cslab-upm/smart-cover/firmware_ESP32/librerias/NTPClient/NTPClient.h

#pragma once

#include "Arduino.h"

#include <Udp.h>

#define SEVENZYYEARS 2208988800UL
#define NTP_PACKET_SIZE 48
#define NTP_DEFAULT_LOCAL_PORT 1337
#define LEAP_YEAR(Y)     ( (Y>0) && !(Y%4) && ( (Y%100) || !(Y%400) ) )


class NTPClient {
  private:
    UDP*          _udp;
    bool          _udpSetup       = false;

    const char*   _poolServerName = "pool.ntp.org"; // Default time server
    int           _port           = NTP_DEFAULT_LOCAL_PORT;
    int           _timeOffset     = 0;

    unsigned long _updateInterval = 60000;  // In ms

    unsigned long _currentEpoc    = 0;      // In s
    unsigned long _lastUpdate     = 0;      // In ms

    byte          _packetBuffer[NTP_PACKET_SIZE];

    void          sendNTPPacket();
    bool          isValid(byte * ntpPacket);

  public:
    NTPClient();
    NTPClient(UDP& udp);
    NTPClient(UDP& udp, int timeOffset);
    NTPClient(UDP& udp, const char* poolServerName);
    NTPClient(UDP& udp, const char* poolServerName, int timeOffset);
    NTPClient(UDP& udp, const char* poolServerName, int timeOffset, unsigned long updateInterval);
    void setUDPClient(UDP& udp);

    /**
     * Starts the underlying UDP client with the default local port
     */
    void begin();

    /**
     * Starts the underlying UDP client with the specified local port
     */
    void begin(int port);

    /**
     * This should be called in the main loop of your application. By default an update from the NTP Server is only
     * made every 60 seconds. This can be configured in the NTPClient constructor.
     *
     * @return true on success, false on failure
     */
    bool update();

    /**
     * This will force the update from the NTP Server.
     *
     * @return true on success, false on failure
     */
    bool forceUpdate();

	int getYear();
	int getDate();
	uint8_t getMonth(unsigned long secs);
    int getDay();
    int getHours();
    int getMinutes();
    int getSeconds();

    /**
     * Changes the time offset. Useful for changing timezones dynamically
     */
    void setTimeOffset(int timeOffset);

    /**
     * Set the update interval to another frequency. E.g. useful when the
     * timeOffset should not be set in the constructor
     */
    void setUpdateInterval(unsigned long updateInterval);

    /**
    * @return secs argument (or 0 for current time) formatted like `hh:mm:ss`
    */
    String getFormattedTime(unsigned long secs = 0);

    /**
     * @return time in seconds since Jan. 1, 1970
     */
    unsigned long getEpochTime();
  
    /**
    * @return secs argument (or 0 for current date) formatted to ISO 8601
    * like `2004-02-12T15:19:21+00:00`
    */
    String getFormattedDate(unsigned long secs = 0);

    /**
     * Stops the underlying UDP client
     */
    void end();

    /**
    * Replace the NTP-fetched time with seconds since Jan. 1, 1970
    */
    void setEpochTime(unsigned long secs);
};
