cslab-upm/smart-cover/firmware_ESP32/tapa_iris/Fotodiodo.h

#include "Sensor.h"

class Fotodiodo: public Sensor{

	public:
		Fotodiodo(int pin1){
			pin=pin1;
		}
    Fotodiodo(){
      
    }
   
		int get_value(){
			value=analogRead(pin);
			return (value);
		}
};
