cslab-upm/smart-cover/firmware_ESP32/tapa_iris/Medidor_de_voltaje.h

#include "Sensor.h"

class Medidor_de_voltaje: public Sensor{

	public:
		Medidor_de_voltaje(int pin1){
			pin=pin1;
		}
    Medidor_de_voltaje(){
      
    }
		int get_value(){
			value=analogRead(pin);
			return (value);
		}
};
